sanbee/Naarad/RPi/NaaradServer/NewServer/NaaradUtils.py

import json;
import time;

def getNodeID(jdict):
    if ("node" in jdict.keys()):
        return jdict['node'];
    if ("node_id" in jdict.keys()):
        return jdict['node_id'];
    raise ValueError("Node ID not found");

def modifyJSON(jdict,keyword,value,op=0):
    #        jdict=json.loads(jsonStr);
    if (op == 0): # add
        for i in range(len(keyword)):
            jdict[keyword[i]]=value[i];
    if (op == 1): # delete
        for i in range(len(keyword)):
            del jdict[keyword[i]];
    return jdict;
    #   return json.dumps(jdict);

def addKey(key,val,jsonStr):
    try:
        jdict=json.loads(jsonStr);
        keywords=[key]; values=[val];
        modifyJSON(jdict,keywords,values,0); # Add time=value
        return json.dumps(jdict);
    except(ValueError) as excpt:
        print("addKey: Not a JSON string: %s"%jsonStr);
        return jsonStr;
    
def addTimeStamp(name,jsonStr): 
    try:
        jdict=json.loads(jsonStr);
        keywords=[name]; values=[time.time()*1000.0];
        modifyJSON(jdict,keywords,values,0); # Add time=value
        return json.dumps(jdict),jdict;
    except(ValueError) as excpt:
        print("Not a JSON string: %s"%jsonStr);
        return jsonStr,json.loads(jsonStr);
        
